TheusHen/Control-Pad/PCB/control-pad.kicad_sch

## KiCad design PCB/control-pad.kicad_sch (2026-02-11)

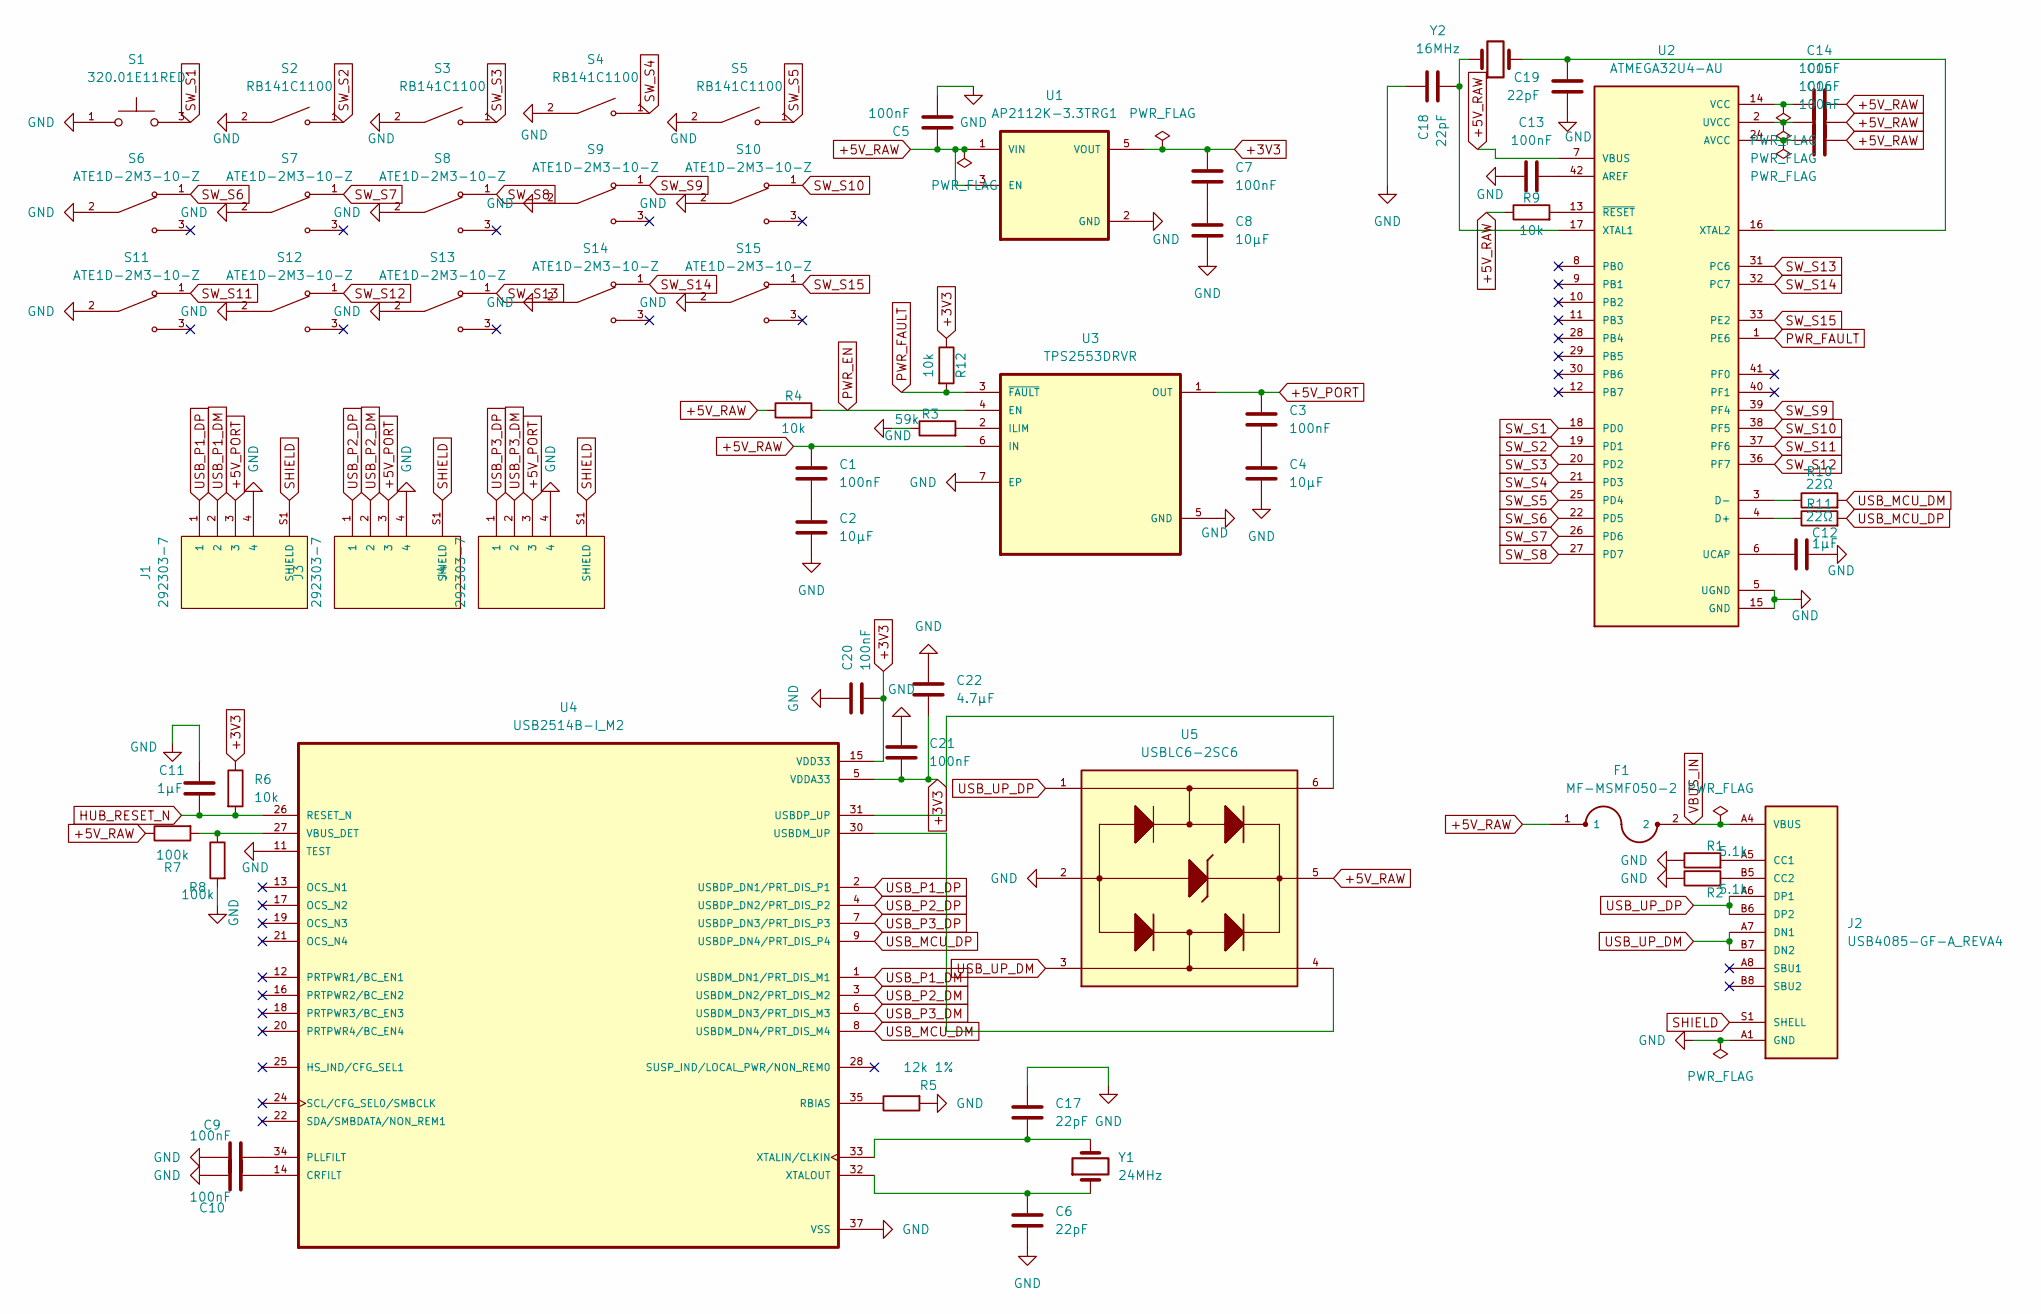
[picture p10: schematic control-pad.kicad_sch]

Parts:
C1, C3, C5, C7, C9, C10, C13, C14, C15, C16, C20, C21: 100nF; C_0603_1608Metric
C2, C4, C8: 10µF; C_0805_2012Metric
C6, C17, C18, C19: 22pF; C_0603_1608Metric
C11, C12: 1µF; C_0603_1608Metric
C22: 4.7µF; C_0805_2012Metric
F1: MF-MSMF050-2; FUSM4632X85
J1, J3, J4: 292303-7; TE_292303-7; PARTREV E12
J2: USB4085-GF-A_REVA4; GCT_USB4085-GF-A_REVA4; PARTREV A4
R1, R2: 5.1k; R_0603_1608Metric
R3: 59k; R_0603_1608Metric
R4, R6, R9, R12: 10k; R_0603_1608Metric
R5: 12k 1%; R_0603_1608Metric
R7, R8: 100k; R_0603_1608Metric
R10, R11: 22Ω; R_0603_1608Metric
S1: 320.01E11RED; SW_320.01E11RED; PARTREV D
S2, S3, S4, S5: RB141C1100; SW_RB141C1100; PARTREV C
S6, S7, S8, S9, S10, S11, S12, S13, S14, S15: ATE1D-2M3-10-Z; SW_ATE1D-2M3-10-Z; PARTREV N/A
U1: AP2112K-3.3TRG1; SOT95P285X140-5N; PARTREV 2-2
U2: ATMEGA32U4-AU; QFP80P1200X1200X120-44N
U3: TPS2553DRVR; SON65P200X200X80-7N
U4: USB2514B-I_M2; QFN50P600X600X100-37N
U5: USBLC6-2SC6; SOT95P280X145-6N
Y1: 24MHz; Crystal_SMD_3225-4Pin_3.2x2.5mm
Y2: 16MHz; Crystal_SMD_3225-4Pin_3.2x2.5mm

Connections:
+3V3: C7.1, C20.2, C21.1, C22.1, R6.1, R12.1, U1.5 (VOUT), U4.5 (VDDA33), U4.10 (VDDA33), U4.15 (VDD33), U4.23 (VDD33), U4.29 (VDDA33), U4.36 (VDDA33)
+5V_PORT: C3.1, J1.3, J3.3, J4.3, U3.1 (OUT)
+5V_RAW: C1.1, C5.1, C14.2, C15.2, C16.2, F1.1, R4.1, R7.1, R9.1, U1.1 (VIN), U1.3 (EN), U2.7 (VBUS), U3.6 (IN), U5.5
GND: C2.2, C4.2, C5.2, C6.2, C8.2, C9.1, C10.1, C11.1, C12.2, C13.1, C17.1, C18.1, C19.1, C20.1, C21.2, C22.2, J1.4, J2.A1 (GND), J2.A12 (GND), J2.B1 (GND), J2.B12 (GND), J3.4, J4.4, R1.1, R2.1, R3.1, R5.2, R8.2, S1.1, S2.2, S3.2, S4.2, S5.2, S6.2, S7.2, S8.2, S9.2, S10.2, S11.2, S12.2, S13.2, S14.2, S15.2, U1.2 (GND), U2.5 (UGND), U2.15 (GND), U2.23 (GND), U2.35 (GND), U2.43 (GND), U3.5 (GND), U3.7 (EP), U4.11 (TEST), U4.37 (VSS), U5.2
HUB_RESET_N: C11.2, R6.2, U4.26 (RESET_N)
unnamed: C1.2, C2.1
unnamed: C3.2, C4.1
unnamed: C6.1, U4.32 (XTALOUT), Y1.1
unnamed: C7.2, C8.1
unnamed: C9.2, U4.34 (PLLFILT)
unnamed: C10.2, U4.14 (CRFILT)
unnamed: C12.1, U2.6 (UCAP)
unnamed: C13.2, U2.42 (AREF)
unnamed: C14.1, U2.14 (VCC), U2.34 (VCC)
unnamed: C15.1, U2.2 (UVCC)
unnamed: C16.1, U2.24 (AVCC), U2.44 (AVCC)
unnamed: C17.2, U4.33 (XTALIN/CLKIN), Y1.2
unnamed: C18.2, U2.17 (XTAL1), Y2.1
unnamed: C19.2, U2.16 (XTAL2), Y2.2
unnamed: J2.A5 (CC1), R1.2
unnamed: J2.B5 (CC2), R2.2
unnamed: R3.2, U3.2 (ILIM)
unnamed: R5.1, U4.35 (RBIAS)
unnamed: R7.2, R8.1, U4.27 (VBUS_DET)
unnamed: R9.2, U2.13 (~RESET)
unnamed: R10.1, U2.3 (D-)
unnamed: R11.1, U2.4 (D+)
unnamed: U4.30 (USBDM_UP), U5.4
unnamed: U4.31 (USBDP_UP), U5.6
PWR_EN: R4.2, U3.4 (EN)
PWR_FAULT: R12.2, U2.1 (PE6), U3.3 (~FAULT)
SHIELD: J1.S1 (SHIELD), J1.S2 (SHIELD), J2.S1 (SHELL), J2.S2 (SHELL), J2.S3 (SHELL), J2.S4 (SHELL), J3.S1 (SHIELD), J3.S2 (SHIELD), J4.S1 (SHIELD), J4.S2 (SHIELD)
SW_S1: S1.3, U2.18 (PD0)
SW_S2: S2.1, U2.19 (PD1)
SW_S3: S3.1, U2.20 (PD2)
SW_S4: S4.1, U2.21 (PD3)
SW_S5: S5.1, U2.25 (PD4)
SW_S6: S6.1, U2.22 (PD5)
SW_S7: S7.1, U2.26 (PD6)
SW_S8: S8.1, U2.27 (PD7)
SW_S9: S9.1, U2.39 (PF4)
SW_S10: S10.1, U2.38 (PF5)
SW_S11: S11.1, U2.37 (PF6)
SW_S12: S12.1, U2.36 (PF7)
SW_S13: S13.1, U2.31 (PC6)
SW_S14: S14.1, U2.32 (PC7)
SW_S15: S15.1, U2.33 (PE2)
USB_MCU_DM: R10.2, U4.8 (USBDM_DN4/PRT_DIS_M4)
USB_MCU_DP: R11.2, U4.9 (USBDP_DN4/PRT_DIS_P4)
USB_P1_DM: J1.2, U4.1 (USBDM_DN1/PRT_DIS_M1)
USB_P1_DP: J1.1, U4.2 (USBDP_DN1/PRT_DIS_P1)
USB_P2_DM: J3.2, U4.3 (USBDM_DN2/PRT_DIS_M2)
USB_P2_DP: J3.1, U4.4 (USBDP_DN2/PRT_DIS_P2)
USB_P3_DM: J4.2, U4.6 (USBDM_DN3/PRT_DIS_M3)
USB_P3_DP: J4.1, U4.7 (USBDP_DN3/PRT_DIS_P3)
USB_UP_DM: J2.A7 (DN1), J2.B7 (DN2), U5.3
USB_UP_DP: J2.A6 (DP1), J2.B6 (DP2), U5.1
VBUS_IN: F1.2, J2.A4 (VBUS), J2.A9 (VBUS), J2.B4 (VBUS), J2.B9 (VBUS)
